LaskaKit/Meteo_Mini/img/1.jpg

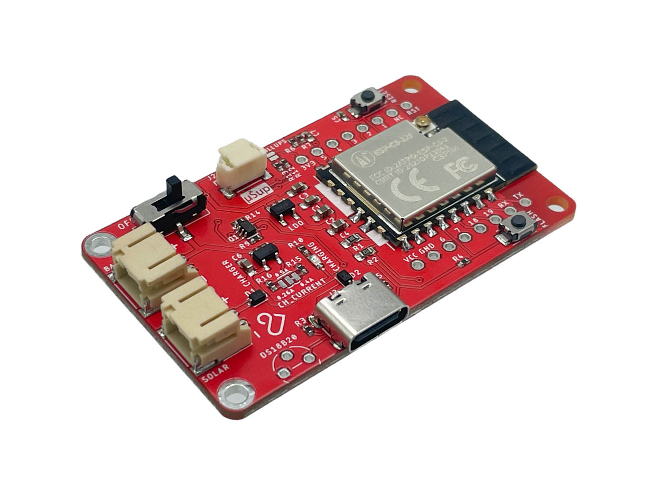
img/1.jpg
