LaskaKit/Meteo_Mini/Production/dutinka-6p-smd-90st-dim.jpg

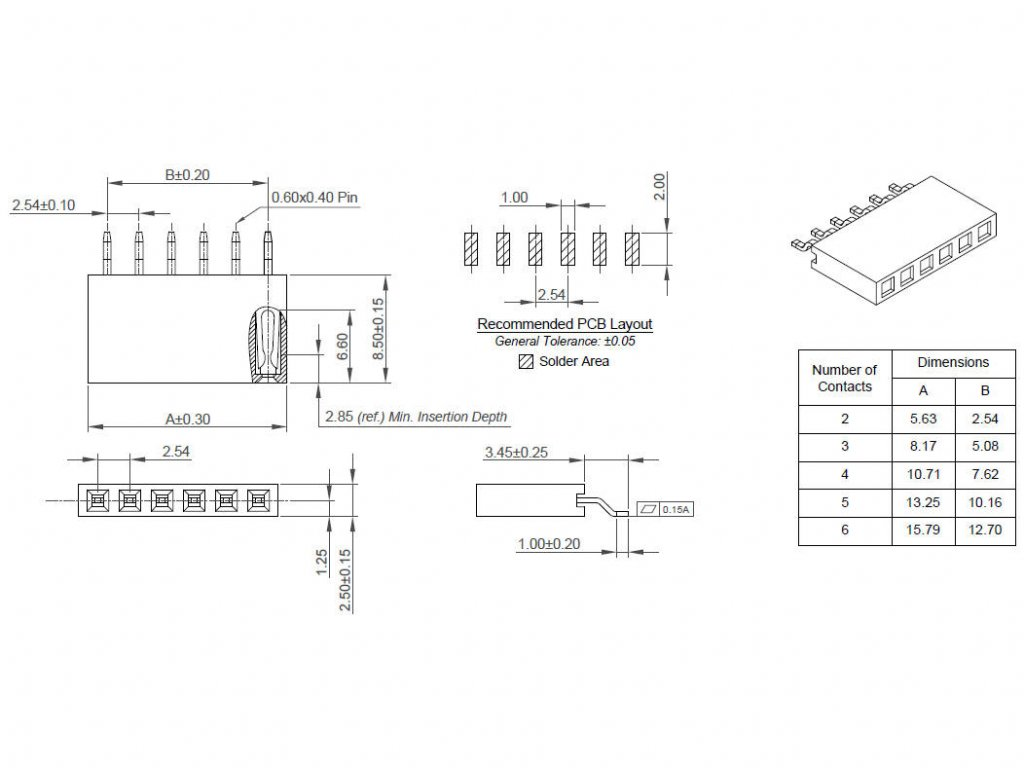
Production/dutinka-6p-smd-90st-dim.jpg
