LaskaKit/Meteo_Mini/SW/Meteo_Mini_ADC_OLED/Meteo_Mini_ADC_OLED.ino

/*
* LaskaKit Meteo Mini board reads voltage on Battery
* Meteo Mini board reads voltage on Battery  
* and sends every 0.5 seconds through UART and LaskaKit 0.91" SSD1306 (SSD1315) OLED i2c display
* 
* Board:   LaskaKit Meteo Mini C3                   https://www.laskakit.cz/laskakit-meteo-mini/
*          LaskaKit Meteo Mini C6                   
* Display: LaskaKit OLED displej 128x32 0.91" I²C   https://www.laskakit.cz/laskakit-oled-displej-128x32-0-91--i--c/
*
* 
* Made by laskakit.cz (c) 2026
*/
#include <SPI.h>
#include <Wire.h>
#include <Adafruit_GFX.h>     // https://github.com/adafruit/Adafruit-GFX-Library
#include <Adafruit_SSD1306.h>

#define Meteo_Mini_C3
//#define Meteo_Mini_C6

#if defined(Meteo_Mini_C3)

  #define ADCpin  0
  #define Power   4
  #define SCL 18
  #define SDA 19 

#elif defined(Meteo_Mini_C6)

  #define ADCpin  3
  #define Power   1
  #define SCL 5
  #define SDA 4 

#endif

#define bDeviderRatio 1.7693877551  // Voltage devider ratio on ADC pin 1MOhm + 1.3MOhm

#define i2c_Address 0x3c

Adafruit_SSD1306 display(128, 32, &Wire, -1);

void setup() {
 Serial.begin(115200);
  pinMode(Power, OUTPUT);
  digitalWrite(Power, HIGH);
  delay(50); // Pause, wait to turn on
  Wire.begin(SDA, SCL);

  while(!Serial);    // time to get serial running
           
  // SSD1306_SWITCHCAPVCC = generate display voltage from 3.3V internally
  if(!display.begin(SSD1306_SWITCHCAPVCC, i2c_Address)) {
    Serial.println(F("SSD1306 allocation failed"));
    for(;;); // Don't proceed, loop forever
  }

  // Show initial display buffer contents on the screen --
  // the library initializes this with an Adafruit splash screen.
  display.display();
  delay(1000); // Pause for 1 second

  display.clearDisplay(); 
  display.setTextColor(SSD1306_WHITE);        // Draw white text
  display.setTextSize(1); 
}

void loop() {

  float bat_voltage = analogReadMilliVolts(ADCpin) * bDeviderRatio / 1000;
  Serial.print("Battery Voltage = " );
  Serial.print(bat_voltage);
  Serial.println("V");

  display.setCursor(0,0);
  display.println((String)"Battery voltage: ");
  display.print(bat_voltage);
  display.println((String)" V");
  display.display(); 
  delay(500);
  display.clearDisplay();
}
